Korotaa/luxm-tre-design_HW-PCB_SW/img/transmission.png

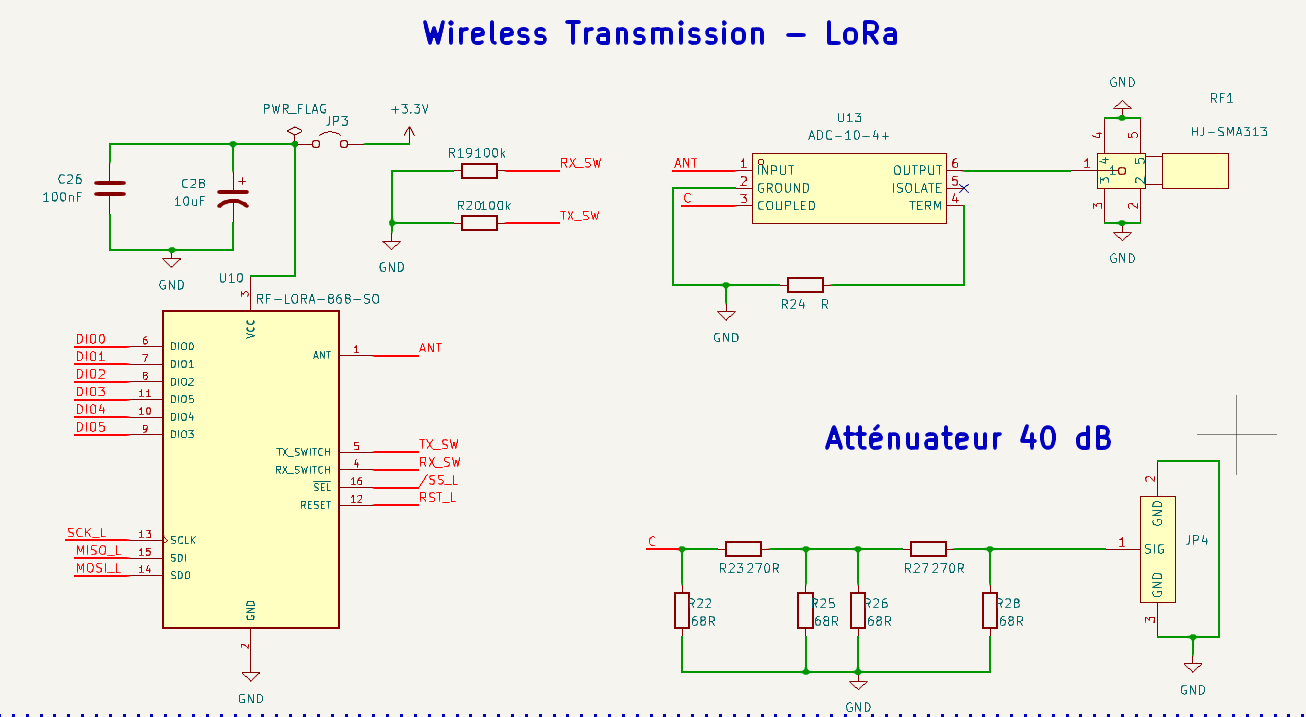
img/transmission.png
