Korotaa/luxm-tre-design_HW-PCB_SW/luxmètre.png

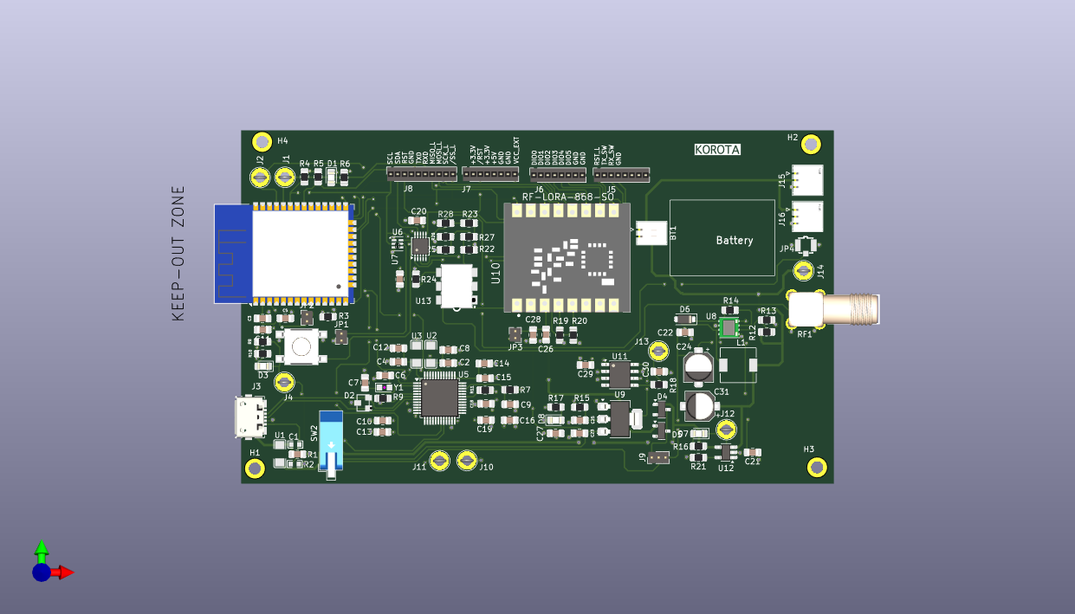
luxmètre.png
