Korotaa/luxm-tre-design_HW-PCB_SW/luxmètre/battery.png

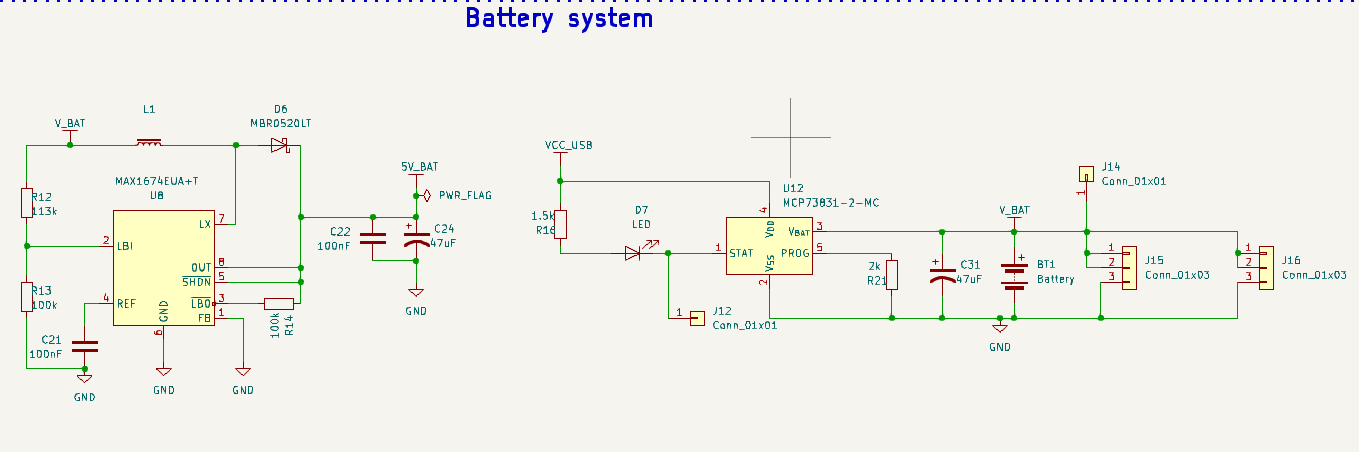
luxmètre/battery.png
