Korotaa/luxm-tre-design_HW-PCB_SW/luxmètre/luxmètre2.png

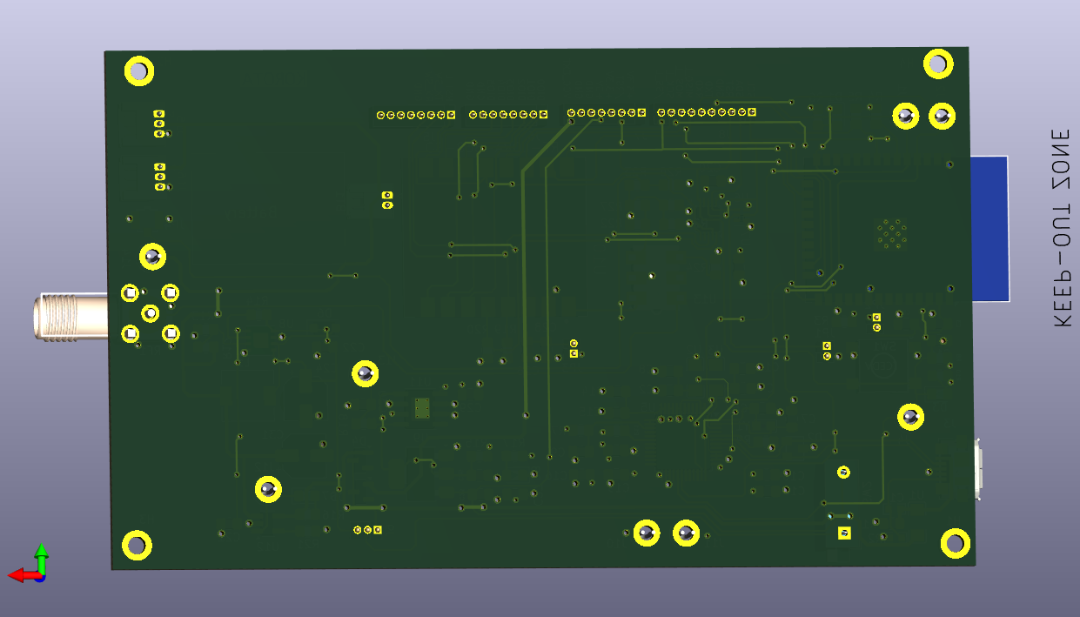
luxmètre/luxmètre2.png
