Korotaa/luxm-tre-design_HW-PCB_SW/Firmware/components/lmic/aes.c

/*
 * Copyright (c) 2014-2016 IBM Corporation.
 * All rights reserved.
 *
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
 * THIS SOFTWARE IS PROVIDED BY THE COPYRIGHT HOLDERS AND CONTRIBUTORS "AS IS" AND
 * ANY EXPRESS OR IMPLIED WARRANTIES, INCLUDING, BUT NOT LIMITED TO, THE IMPLIED
 * WARRANTIES OF MERCHANTABILITY AND FITNESS FOR A PARTICULAR PURPOSE ARE
 * DISCLAIMED. IN NO EVENT SHALL <COPYRIGHT HOLDER> BE LIABLE FOR ANY
 * DIRECT, INDIRECT, INCIDENTAL, SPECIAL, EXEMPLARY, OR CONSEQUENTIAL DAMAGES
 * (INCLUDING, BUT NOT LIMITED TO, PROCUREMENT OF SUBSTITUTE GOODS OR SERVICES;
 * LOSS OF USE, DATA, OR PROFITS; OR BUSINESS INTERRUPTION) HOWEVER CAUSED AND
 * ON ANY THEORY OF LIABILITY, WHETHER IN CONTRACT, STRICT LIABILITY, OR TORT
 * (INCLUDING NEGLIGENCE OR OTHERWISE) ARISING IN ANY WAY OUT OF THE USE OF THIS
 * SOFTWARE, EVEN IF ADVISED OF THE POSSIBILITY OF SUCH DAMAGE.
 */

#include "oslmic.h"

#define AES_MICSUB 0x30 // internal use only

static const u4_t AES_RCON[10] = { 
    0x01000000, 0x02000000, 0x04000000, 0x08000000, 0x10000000, 
    0x20000000, 0x40000000, 0x80000000, 0x1B000000, 0x36000000
};

static const u1_t AES_S[256] = {
  0x63, 0x7C, 0x77, 0x7B, 0xF2, 0x6B, 0x6F, 0xC5, 0x30, 0x01, 0x67, 0x2B, 0xFE, 0xD7, 0xAB, 0x76, 
  0xCA, 0x82, 0xC9, 0x7D, 0xFA, 0x59, 0x47, 0xF0, 0xAD, 0xD4, 0xA2, 0xAF, 0x9C, 0xA4, 0x72, 0xC0, 
  0xB7, 0xFD, 0x93, 0x26, 0x36, 0x3F, 0xF7, 0xCC, 0x34, 0xA5, 0xE5, 0xF1, 0x71, 0xD8, 0x31, 0x15, 
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
u4_t AESAUX[16/sizeof(u4_t)];
u4_t AESKEY[11*16/sizeof(u4_t)];

// generate 1+10 roundkeys for encryption with 128-bit key
// read 128-bit key from AESKEY in MSBF, generate roundkey words in place
static void aesroundkeys () {
    int i;
    u4_t b;

    for( i=0; i<4; i++) {
        AESKEY[i] = swapmsbf(AESKEY[i]);
    }
    
    b = AESKEY[3];
    for( ; i<44; i++ ) {
        if( i%4==0 ) {
            // b = SubWord(RotWord(b)) xor Rcon[i/4]
            b = (AES_S[u1(b >> 16)] << 24) ^
                (AES_S[u1(b >>  8)] << 16) ^
                (AES_S[u1(b)      ] <<  8) ^
                (AES_S[   b >> 24 ]      ) ^
                 AES_RCON[(i-4)/4];
        }
        AESKEY[i] = b ^= AESKEY[i-4];
    }
}

u4_t os_aes (u1_t mode, xref2u1_t buf, u2_t len) {
        
        aesroundkeys();

        if( mode & AES_MICNOAUX ) {
            AESAUX[0] = AESAUX[1] = AESAUX[2] = AESAUX[3] = 0;
        } else {
            AESAUX[0] = swapmsbf(AESAUX[0]);
            AESAUX[1] = swapmsbf(AESAUX[1]);
            AESAUX[2] = swapmsbf(AESAUX[2]);
            AESAUX[3] = swapmsbf(AESAUX[3]);
        }

        while( (signed char)len > 0 ) {
            u4_t a0=0, a1=0, a2=0, a3=0;
            u4_t t0=0, t1=0, t2=0, t3=0;
            u4_t *ki, *ke;

            // load input block
            if( (mode & AES_CTR) || ((mode & AES_MIC) && (mode & AES_MICNOAUX)==0) ) { // load CTR block or first MIC block
                a0 = AESAUX[0];
                a1 = AESAUX[1];
                a2 = AESAUX[2];
                a3 = AESAUX[3];
            }
            else if( (mode & AES_MIC) && len <= 16 ) { // last MIC block
                a0 = a1 = a2 = a3 = 0; // load null block
                mode |= ((len == 16) ? 1 : 2) << 4; // set MICSUB: CMAC subkey K1 or K2
            } else
        LOADDATA: { // load data block (partially)
                for(t0=0; t0<16; t0++) {
                    t1 = (t1<<8) | ((t0<len) ? buf[t0] : (t0==len) ? 0x80 : 0x00);
                    if((t0&3)==3) {
                        a0 = a1;
                        a1 = a2;
                        a2 = a3;
                        a3 = t1;
                    }
                } 
                if( mode & AES_MIC ) {
                    a0 ^= AESAUX[0];
                    a1 ^= AESAUX[1];
                    a2 ^= AESAUX[2];
                    a3 ^= AESAUX[3];
                }
            }

            // perform AES encryption on block in a0-a3
            ki = AESKEY;
            ke = ki + 8*4;
            a0 ^= ki[0];
            a1 ^= ki[1];
            a2 ^= ki[2];
            a3 ^= ki[3];
            do {
                AES_key4 (t1,t2,t3,t0,4);
                AES_expr4(t1,t2,t3,t0,a0);
                AES_expr4(t2,t3,t0,t1,a1);
                AES_expr4(t3,t0,t1,t2,a2);
                AES_expr4(t0,t1,t2,t3,a3);

                AES_key4 (a1,a2,a3,a0,8);
                AES_expr4(a1,a2,a3,a0,t0);
                AES_expr4(a2,a3,a0,a1,t1);
                AES_expr4(a3,a0,a1,a2,t2);
                AES_expr4(a0,a1,a2,a3,t3);
            } while( (ki+=8) < ke );

            AES_key4 (t1,t2,t3,t0,4);
            AES_expr4(t1,t2,t3,t0,a0);
            AES_expr4(t2,t3,t0,t1,a1);
            AES_expr4(t3,t0,t1,t2,a2);
            AES_expr4(t0,t1,t2,t3,a3);

            AES_expr(a0,t0,t1,t2,t3,8);
            AES_expr(a1,t1,t2,t3,t0,9);
            AES_expr(a2,t2,t3,t0,t1,10);
            AES_expr(a3,t3,t0,t1,t2,11);
            // result of AES encryption in a0-a3

            if( mode & AES_MIC ) {
                if( (t1 = (mode & AES_MICSUB) >> 4) != 0 ) { // last block
                    do {
                        // compute CMAC subkey K1 and K2
                        t0 = a0 >> 31; // save MSB
                        a0 = (a0 << 1) | (a1 >> 31);
                        a1 = (a1 << 1) | (a2 >> 31);
                        a2 = (a2 << 1) | (a3 >> 31);
                        a3 = (a3 << 1);
                        if( t0 ) a3 ^= 0x87;
                    } while( --t1 );

                    AESAUX[0] ^= a0;
                    AESAUX[1] ^= a1;
                    AESAUX[2] ^= a2;
                    AESAUX[3] ^= a3;
                    mode &= ~AES_MICSUB;
                    goto LOADDATA;
                } else {
                    // save cipher block as new iv
                    AESAUX[0] = a0;
                    AESAUX[1] = a1;
                    AESAUX[2] = a2;
                    AESAUX[3] = a3;
                }
            } else { // CIPHER
                if( mode & AES_CTR ) { // xor block (partially)
                    t0 = (len > 16) ? 16: len;
                    for(t1=0; t1<t0; t1++) {
                        buf[t1] ^= (a0>>24);
                        a0 <<= 8;
                        if((t1&3)==3) {
                            a0 = a1;
                            a1 = a2;
                            a2 = a3;
                        }
                    }
                    // update counter
                    AESAUX[3]++;
                } else { // ECB
                    // store block
                    msbf4_write(buf+0,  a0);
                    msbf4_write(buf+4,  a1);
                    msbf4_write(buf+8,  a2);
                    msbf4_write(buf+12, a3);
                }
            }

            // update block state
            if( (mode & AES_MIC)==0 || (mode & AES_MICNOAUX) ) {
                buf += 16;
                len -= 16;
            }
            mode |= AES_MICNOAUX;
        }
        return AESAUX[0];
}
