Korotaa/luxm-tre-design_HW-PCB_SW/Firmware/main/lorawan_cnf.h

#ifndef _LORAWAN_CNF_H
#define _LORAWAN_CNF_H


// Definition des ports pour capteur eid430

#define LORAWAN_PORT_TOR            1
#define LORAWAN_PORT_Pot            2
#define LORAWAN_PORT_Lum            3
#define LORAWAN_PORT_TPH            4
#define LORAWAN_PORT_GyrAcc         5
#define LORAWAN_PORT_Magneto        6
#define LORAWAN_PORT_Pouls          7
#define LORAWAN_PORT_HTR            8
#define LORAWAN_PORT_ChaineCarac    9

#define LORAWAN_PORT_EXT_Jauge      10
#define LORAWAN_PORT_EXT_Meteo      11

//#define LORAWAN_PORT_EXT_abc...   0x1x  a coder par l'utilisateur  abc: nomproject x numero du port du project en LoRaWAN



#endif
