Korotaa/luxm-tre-design_HW-PCB_SW/Firmware/main/ttn.h

#ifndef __ttn_h
#define __ttn_h


//network session key de ttn    6DF8BF7E59D7E3FD87D5E38BE842AC46
//u1_t NWKSKEY[16] = { 0x6d, 0xf8, 0xbf, 0x7e, 0x59, 0xd7, 0xe3, 0xfd, 0x87, 0xd5, 0xe3, 0x8b, 0xe8, 0x42, 0xac, 0x46 }; 
//lorawan                        2b7e151628aed2a6abf7158809cf4f3c
u1_t NWKSKEY[16] = { 0x2b, 0x7e, 0x15, 0x16, 0x28, 0xae, 0xd2, 0xa6, 0xab, 0xf7, 0x15, 0x88, 0x09, 0xcf, 0x4f, 0x3c }; 

// app key de ttn               09D4E5F2F1F50B4F02C0DA09F214D936
//u1_t APPSKEY[16] = { 0x09, 0xd4, 0xe5, 0xf2, 0xf1, 0xf5, 0x0b, 0x4f, 0x02, 0xc0, 0xda, 0x09, 0xf2, 0x14, 0xD9, 0x36};
//lorawan                       2b7e151628aed2a6abf7158809cf4f3c
u1_t APPSKEY[16] = { 0x2b, 0x7e, 0x15, 0x16, 0x28, 0xae, 0xd2, 0xa6, 0xab, 0xf7, 0x15, 0x88, 0x09, 0xcf, 0x4f, 0x3c};

// Mettre de DEVADDR de ttn
//u4_t DEVADDR = 0x26011EBF;
//lorawan
u4_t DEVADDR = 0x26011141;

// Mettre de DEVEUI de ttn et LoraWan F1F2F34301000001
u1_t DEVEUI[8]= { 0xF1,0xF2,0xF3,0x43,0x01,0x00,0x00,0x01};

// Mettre de code EUI de ttn dans la variable APPEUI du ttn
u1_t APPEUI[8]= { 0x70, 0xB3,0xD5,0x7E,0xD0,0x02,0x23,0x9D};
//u1_t APPEUI[8]= { 0x70, 0xB3,0xD5,0x7E,0xD0,0x02,0x49,0x96}; 

#endif
